SamsHomeAutomation/HACH/3D RENDERS/4chPro Adapter with IC.jpg

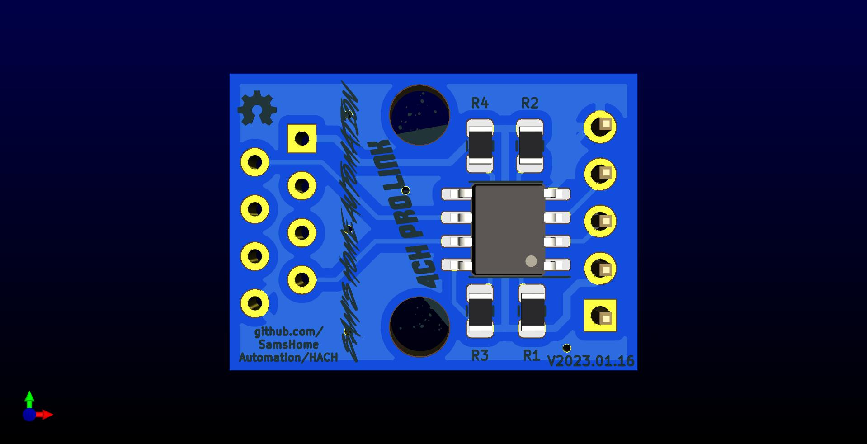
3D RENDERS/4chPro Adapter with IC.jpg
